ilPez00/CyclUno/cad/cycluno_case/CyclUnoCase_v08.FCStd

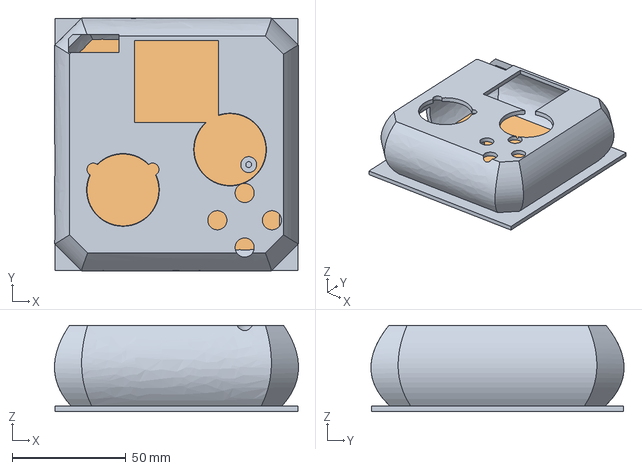
[picture p15: CAD file, 2026-07-17, an earlier design]
cad/cycluno_case/CyclUnoCase_v08.FCStd
107.3 x 111.3 x 38.0 mm
Base_v08
Lid_v08
