ilPez00/CyclUno/cad/cycluno_case/CyclUnoCase_v03.FCStd

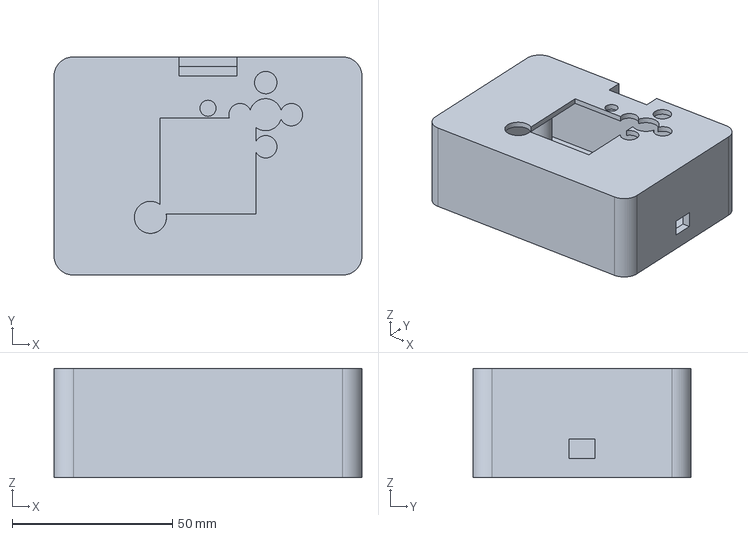
[picture p16: CAD file, 2026-07-17, an earlier design]
cad/cycluno_case/CyclUnoCase_v03.FCStd
96.0 x 68.0 x 34.0 mm
