ilPez00/CyclUno/cad/cycluno_case/CyclUnoCase_v05.FCStd

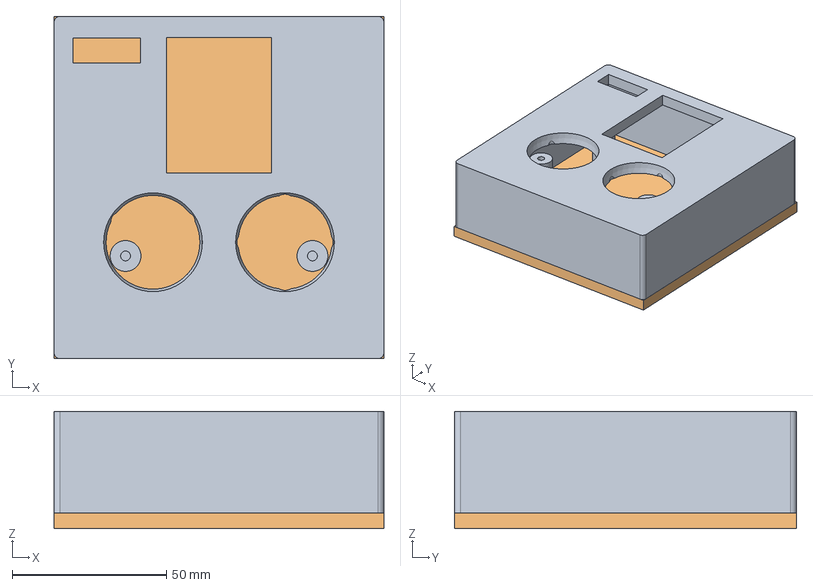
[picture p17: CAD file, 2026-07-16, an earlier design]
cad/cycluno_case/CyclUnoCase_v05.FCStd
107.0 x 111.0 x 38.0 mm
Base_v05
Lid_v05
